MattSpot10/Artificer-A1-Single-Board-Computer/PCB/Simulations/PSU, voltage, polarity, and transient protection/Draft5.asc

D1: zener; EDZV10B
D2: zener; BZX84C12L
Q1: npn; 2N2222
Q2: npn; 2N2222
R1: res; 100k
R2: res; 100k
R3: res; 1
R4: res; 10k
R6: res; 10k
R7: res; 10k
R8: res; 100
R9: res; 10k
U1: SSM3J352F_G0_00
U2: SSM3J352F_G0_00
V1: voltage; SINE(0 13 60)
Named nets: 0
.dc V1 -20 20 .01
.tran 1
