MattSpot10/Artificer-A1-Single-Board-Computer/PCB/Simulations/PSU, voltage, polarity, and transient protection/Draft4.asc

C1: cap; 1µF
D1: zener; BZX84C10L
D2: zener; BZX84C12L
Q1: npn; 2N2222
Q2: npn; 2N2222
R1: res; 100k
R2: res; 100k
R3: res; 60
R4: res; 10k
R5: res; 10k
R6: res; 10k
R7: res; 10k
R8: res; 5k
U1: SSM3J352F_G0_00
U2: SSM3J352F_G0_00
V1: voltage; SINE(0 20 60)
Named nets: 0
.dc V1 -20 20 .1
.tran 1
